makser-cisial/Qlubi-light-pal/Product photos/DSC00004.JPG

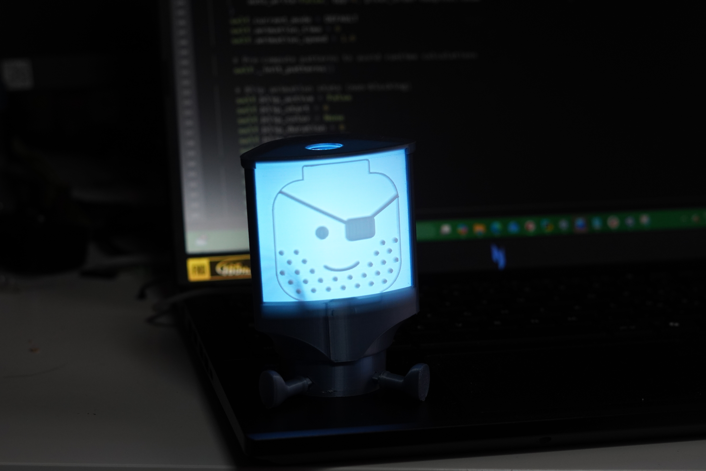
Product photos/DSC00004.JPG
